den-kozlov/ProForge300/Config Files/calibrate-offsets.cfg

#########################################################################################
##################### ProForge 300 Print Head Calibration Config ########################
#########################################################################################

#config file version v1.0.0
#release date: 18.12.2024


[tools_calibrate]
pin: ^PC0
travel_speed: 20  # mms to travel sideways for XY probing
spread: 7  # mms to travel down from top for XY probing
lower_z: 0.50  # The speed (in mm/sec) to move tools down onto the probe
speed: 2  # The speed (in mm/sec) to retract between probes
lift_speed: 4  # Z Lift after probing done, should be greater than any Z variance between tools
final_lift_z: 6 
sample_retract_dist:2
samples_tolerance:0.1
samples:2
samples_result: median # median, average
# Settings for nozzle probe calibration - optional.

probe: probe # name of the nozzle probe to use
trigger_to_bottom_z: 1.0 # Offset from probe trigger to vertical motion bottoms out. 
# decrease if the nozzle is too high, increase if too low.


[gcode_macro _CALIBRATE_MOVE_OVER_PROBE]
gcode:
    BED_MESH_CLEAR
    G0 Z26 F10000 # UPDATE THIS WITH YOUR POSITION
    G0 X80 Y270 F10000  # UPDATE THIS WITH YOUR POSITION



[gcode_macro CALIBRATE_TOOL_OFFSETS]
gcode:
    {% set svv = printer.save_variables.variables %}
    {% set tool_count = svv.active_tools %}
    # Handle different tool count scenarios explicitly
    {% if tool_count == 0 %}
      RESPOND MSG="No print heads detected. Check configuration."
    {% elif tool_count == 1 %}
      RESPOND MSG="Only one print head installed. Calibration requires more than one."
    {% elif tool_count == 2 %}
      RESPOND MSG="Detected 2 print heads. Heating both to 200°C before calibration."
      T0
      M104 S200  # Heat Tool 0 to 200°C
      T1
      M104 S200  # Heat Tool 1 to 200°C
      T0
      M109 S200  # Wait until Tool 0 is 200°C
      T1
      M109 S200  # Wait until Tool 1 is 200°C
      RESPOND MSG="Starting calibration for 2 print heads."
      G28
      _CAL_SELECT_T0
      _CALIBRATE_MOVE_OVER_PROBE
      TOOL_LOCATE_SENSOR
      M104 S0
      SAVE_GCODE_STATE NAME=SENSOR_LOCATION
      _CAL_DOCK_T0
      {% for tool in [1] %}
        _CAL_SELECT_T{tool}
        RESTORE_GCODE_STATE NAME=SENSOR_LOCATION MOVE=1 MOVE_SPEED=150
        TOOL_CALIBRATE_TOOL_OFFSET_{tool}
        M104 S0
        _CAL_DOCK_T{tool}
      {% endfor %}
      SAVE_CONFIG
    {% elif tool_count == 3 %}
      RESPOND MSG="Detected 3 print heads. Heating all to 200°C before calibration."
      T0
      M104 S200  # Heat Tool 0 to 200°C
      T1
      M104 S200  # Heat Tool 1 to 200°C
      T2
      M104 S200  # Heat Tool 2 to 200°C
      T0
      M109 S200  # Wait until Tool 0 is 200°C
      T1
      M109 S200  # Wait until Tool 1 is 200°C
      T2
      M109 S200  # Wait until Tool 2 is 200°C
      RESPOND MSG="Starting calibration for 3 print heads."
      G28
      _CAL_SELECT_T0
      _CALIBRATE_MOVE_OVER_PROBE
      TOOL_LOCATE_SENSOR
      M104 S0
      SAVE_GCODE_STATE NAME=SENSOR_LOCATION
      _CAL_DOCK_T0
      {% for tool in [1, 2] %}
        _CAL_SELECT_T{tool}
        RESTORE_GCODE_STATE NAME=SENSOR_LOCATION MOVE=1 MOVE_SPEED=150
        TOOL_CALIBRATE_TOOL_OFFSET_{tool}
        M104 S0
        _CAL_DOCK_T{tool}
      {% endfor %}
      SAVE_CONFIG
    {% else %}
      RESPOND MSG="Error: Unexpected tool count. Check configuration."
    {% endif %}



### Toolhead Select and Dock Macros ###

[gcode_macro _CAL_SELECT_T0]
gcode:
  {% set svv = printer.save_variables.variables %}
  T0
  G0 Y{svv.zero_select_y} F12000
  G0 X{svv.zero_select_x + 7} F12000
  G0 X{svv.zero_select_x} F1000
  G0 Y{svv.zero_dock_y} F1000
  _SERVO_SELECT
  G0 X{svv.zero_select_x + 8} F9000
  _WIPE
  G0 X0 F9000
  _OFFSET_RESET

[gcode_macro _CAL_DOCK_T0]
gcode:
  {% set svv = printer.save_variables.variables %}
  _OFFSET_RESET
  G0 Y{svv.zero_dock_y} F12000
  G0 X{svv.zero_dock_x + 31}  F12000
  G0 X{svv.zero_dock_x} F8000
  _SERVO_DOCK
  G0 Y{svv.zero_select_y} F4000
  G0 X{svv.zero_dock_x + 15} F12000




[gcode_macro _CAL_SELECT_T1]
gcode:
  {% set svv = printer.save_variables.variables %}
  T1
  G0 Y{svv.one_select_y} F12000
  G0 X{svv.one_select_x + 7} F12000
  G0 X{svv.one_select_x} F1000
  G0 Y{svv.one_dock_y} F1000
  _SERVO_SELECT
  G0 X{svv.one_select_x + 8} F9000
  _WIPE
  G0 X0 F9000
  _OFFSET_RESET

[gcode_macro _CAL_DOCK_T1]
gcode:
  {% set svv = printer.save_variables.variables %}
  _OFFSET_RESET
  G0 Y{svv.one_dock_y} F12000
  G0 X{svv.one_dock_x + 31}  F12000
  G0 X{svv.one_dock_x} F8000
  _SERVO_DOCK
  G0 Y{svv.one_select_y} F4000
  G0 X{svv.one_dock_x + 15} F12000




[gcode_macro _CAL_SELECT_T2]
gcode:
  {% set svv = printer.save_variables.variables %}
  T2
  G0 Y{svv.two_select_y} F12000
  G0 X{svv.two_select_x + 7} F12000
  G0 X{svv.two_select_x} F1000
  G0 Y{svv.two_dock_y} F1000
  _SERVO_SELECT
  G0 X{svv.two_select_x + 8} F9000
  _WIPE
  G0 X0 F9000
  _OFFSET_RESET

[gcode_macro _CAL_DOCK_T2]
gcode:
  {% set svv = printer.save_variables.variables %}
  _OFFSET_RESET
  G0 Y{svv.two_dock_y} F12000
  G0 X{svv.two_dock_x + 31}  F12000
  G0 X{svv.two_dock_x} F8000
  _SERVO_DOCK
  G0 Y{svv.two_select_y} F4000
  G0 X{svv.two_dock_x + 15} F12000
